Eli-S-Bridge/ETAG_AOS2017/ETAG_U2270B_Jul2017/logger.cpp

#include "Arduino.h"
#include "logger.h" 

#include <SD.h>


void logger::load_settings(){
  //Serial.println("loading settings");
  String current_setting = "";
  String value = "";
  
  if (!SD.begin(10)) {
    const String error_msg = "SD card not found!";
    Serial.println(error_msg);
    return;
  }
  File settings = SD.open("settings.txt");
  if (settings) {
    char letter;
    while (settings.available()) {
      letter = settings.read();
      switch (letter) {
        case '#':
          while (settings.available() && letter != '\n' && letter != '\r') {
            letter = settings.read();
          }
          break;
        case '\t':
        case '\n':
        case '\r':
        case ' ': //do nothing with spaces new lines and tabs
          break;
        case ':':
          while (settings.available() && letter != ';') { //read in setting value
            value += settings.read();
            letter = settings.read();
          }

          set_setting(current_setting, value);
          value = "";
          current_setting = "";
          break;
        default:
          current_setting += letter;
          break;
      }
    }
    settings.close();
  } else {
    // if the file didn't open, print an error:
    //const String error_msg = "error opening settings.txt";
    //Serial.println(error_msg);
  }
}

logger::logger(){
    logger(5,2,1);
}
//initialize the RFIDuino object and set the pins correctlly based on hardware version
//logger::logger(int idemod,int ishd,int imod,int irdyclk){
logger::logger(int idemod,int imod,int irdyclk){
  
  //RFID related pins
    demodOut = idemod;//5;
    //shd = ishd;//4;
    mod = imod;//2;
    rdyClk = irdyclk;//1;
  //set pin modes on RFID pins
  pinMode(mod, OUTPUT);
  //pinMode(shd, OUTPUT);
  //pinMode(demodOut, INPUT);
  pinMode(demodOut, INPUT_PULLUP);  //Use pullup resistors for U2270B
  pinMode(rdyClk, INPUT);

  //set shd and MOD low to prepare for reading
  //digitalWrite(shd, LOW);
  //digitalWrite(shd, HIGH);  //SHD pin should be high to turn on U2270B 
  digitalWrite(mod, LOW);
}

//Manchester decode. Supply the function an array to store the tags ID in
bool logger::decodeTag(unsigned char *buf){
  unsigned char i = 0;
  unsigned short timeCount;
  unsigned char timeOutFlag = 0;
  unsigned char row, col;
  unsigned char row_parity;
  unsigned char col_parity[5];
  unsigned char dat;
  unsigned char searchCount = 0;
  unsigned char j;
  while(1){
    timeCount = 0;
    while(0 == digitalRead(demodOut)){//watch for demodOut to go low
      if(timeCount >= TIMEOUT){ //if we pass TIMEOUT milliseconds, break out of the loop
        break;
      } else {
        timeCount++;
      }
    } if (timeCount >= 600) {
      return false;
    }
    timeCount = 0;
    delayMicroseconds(DELAYVAL);
    if(digitalRead(demodOut)) {
      for(i = 0; i < 8; i++) {// 9 header bits
        timeCount = 0; //restart counting
        while(1 == digitalRead(demodOut)) {//while DEMOD out is high
          if(timeCount == TIMEOUT){
            timeOutFlag = 1;
            break;
          } else {
            timeCount++;
          }
        }
        if(timeOutFlag) {
          break;
        } else {
          delayMicroseconds(DELAYVAL);
          if( 0 == digitalRead(demodOut) ){
            break;
          }
        }
      }
      if(timeOutFlag){
        timeOutFlag = 0;
        return false;
      }
      if(i == 8){ //Receive the data
        timeOutFlag = 0;
        timeCount = 0;
        while(1 == digitalRead(demodOut)){
          if(timeCount == TIMEOUT){
            timeOutFlag = 1;
            break;
          } else {
            timeCount++;
          }
          if(timeOutFlag){
            timeOutFlag = 0;
            return false;
          }
        }
        col_parity[0] = col_parity[1] = col_parity[2] = col_parity[3] = col_parity[4] = 0;
        for(row = 0; row < 11; row++){
          row_parity = 0;
          j = row >> 1;
          for(col = 0, row_parity = 0; col < 5; col++){
            delayMicroseconds(DELAYVAL);
            if(digitalRead(demodOut)){
              dat = 1;
            } else {
              dat = 0;
            }
            if(col < 4 && row < 10){
              buf[j] <<= 1;
              buf[j] |= dat;
            }
            row_parity += dat;
            col_parity[col] += dat;
            timeCount = 0;
            while(digitalRead(demodOut) == dat){
              if(timeCount == TIMEOUT){
                timeOutFlag = 1;
                break;
              } else {
                timeCount++;
              }
            }
            if(timeOutFlag) {
              break;
            }
          }
          if(row < 10){
            if((row_parity & 0x01) || timeOutFlag){ //Row parity
              timeOutFlag = 1;
              break;
            }
          }
        }

        if( timeOutFlag || (col_parity[0] & 0x01) || (col_parity[1] & 0x01) || (col_parity[2] & 0x01) || (col_parity[3] & 0x01) ){ //Column parity
          timeOutFlag = 0;
          return false;
        } else {
          return true;
        }
      }//end if(i==8)
      return false;
    }//if(digitalRead(demodOut))
  } //while(1)
};

//function to compare 2 byte arrays. Returns true if the two arrays match, false of any numbers do not match
bool logger::compareTagData(byte *tagData1, byte *tagData2){
  for(int j = 0; j < 5; j++){
    if (tagData1[j] != tagData2[j]){
      return false; //if any of the ID numbers are not the same, return a false
    }
  }
  return true;  //all id numbers have been verified
}

//function to transfer one byte array to a secondary byte array.
//source -> tagData
//destination -> tagDataBuffer
void logger::transferToBuffer(byte *tagData, byte *tagDataBuffer){
  for(int j = 0; j < 5; j++){
    tagDataBuffer[j] = tagData[j];
  }
}

bool logger::scanForTag(byte *tagData){
  static byte tagDataBuffer[5];      //A Buffer for verifying the tag data. 'static' so that the data is maintained the next time the loop is called
  static int readCount = 0;          //the number of times a tag has been read. 'static' so that the data is maintained the next time the loop is called
  boolean verifyRead = false; //true when a tag's ID matches a previous read, false otherwise
  boolean tagCheck = false;   //true when a tag has been read, false otherwise
  tagCheck = decodeTag(tagData); //run the decodetag to check for the tag
  if (tagCheck == true) //if 'true' is returned from the decodetag function, a tag was succesfully scanned
  {
    readCount++;      //increase count since we've seen a tag
    if(readCount == 1) //if have read a tag only one time, proceed
    {
      transferToBuffer(tagData, tagDataBuffer);  //place the data from the current tag read into the buffer for the next read
    }
    else if(readCount == 2) //if we see a tag a second time, proceed
    {
      verifyRead = compareTagData(tagData, tagDataBuffer); //run the checkBuffer function to compare the data in the buffer (the last read) with the data from the current read
      if (verifyRead == true) //if a 'true' is returned by compareTagData, the current read matches the last read
      {
        readCount = 0; //because a tag has been succesfully verified, reset the readCount to '0' for the next tag
        return true;
      }
    }
  }
  else
  {
    return false;
  }
}
